c3h899/Diffuse_Light_Panel/Ideal_Model/3000-4500-6000 Response.png

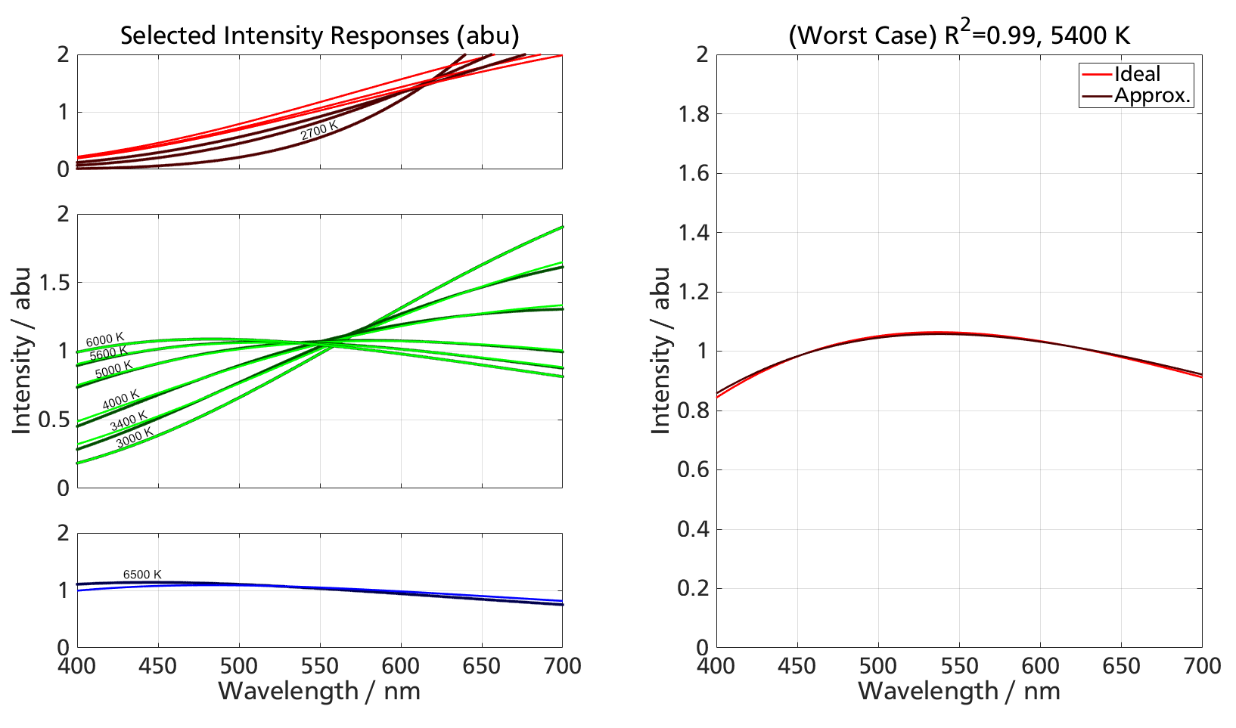
Ideal_Model/3000-4500-6000 Response.png
