c3h899/Diffuse_Light_Panel/Tri-Color LED/Preview/Cake-Pan-Ring.jpg

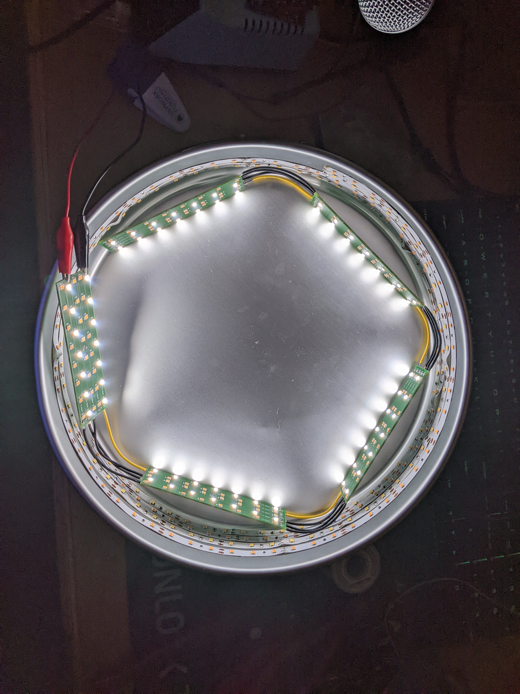
Tri-Color LED/Preview/Cake-Pan-Ring.jpg
