c3h899/Diffuse_Light_Panel/Tri-Color LED/Preview/Proto-Module.PNG

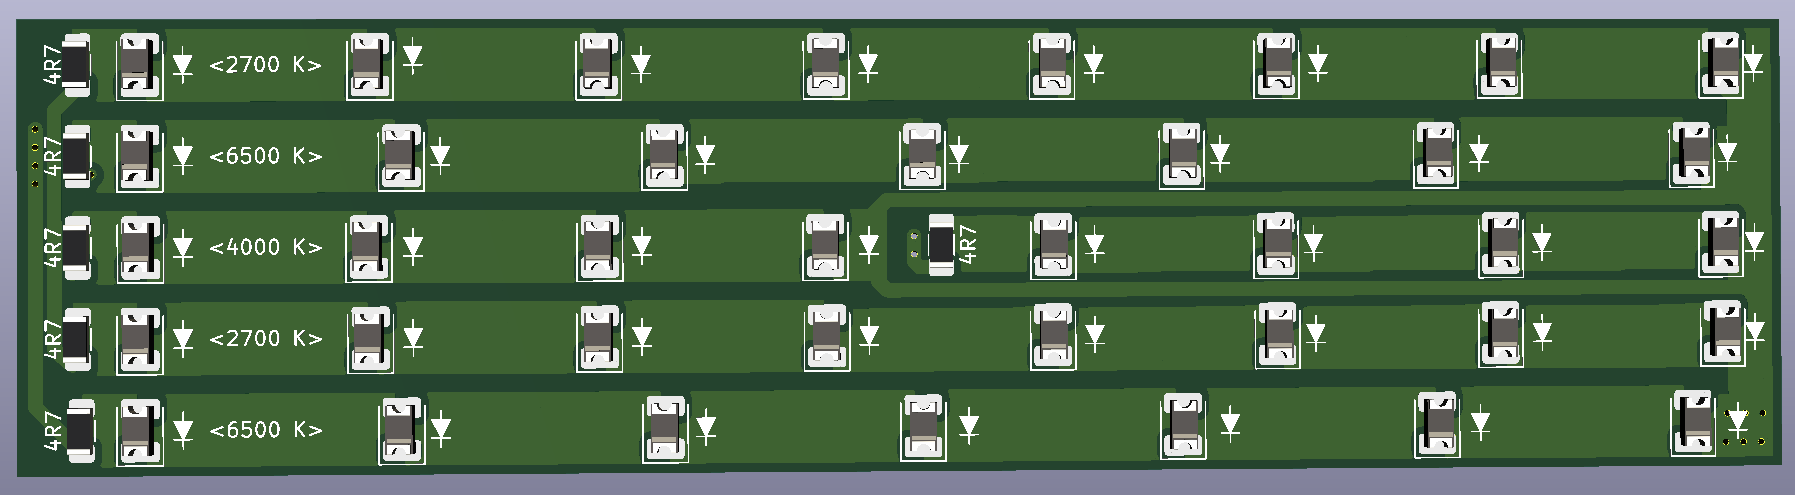
Tri-Color LED/Preview/Proto-Module.PNG
