c3h899/Diffuse_Light_Panel/LED_Measurements/5-foot Strip.PNG

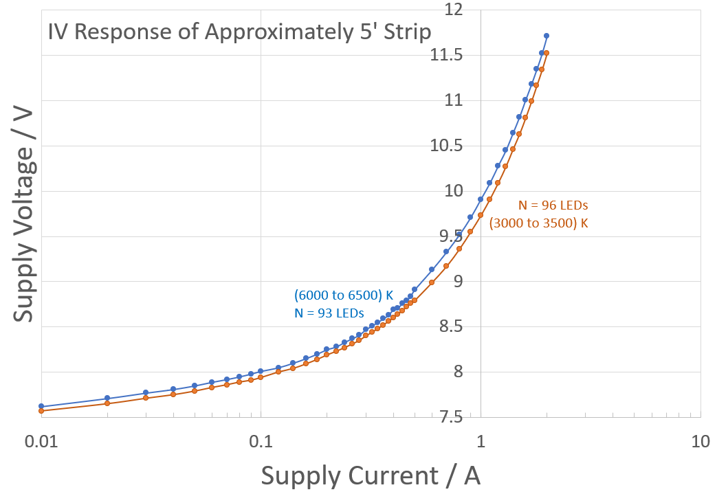
LED_Measurements/5-foot Strip.PNG
