c3h899/Diffuse_Light_Panel/LED_Measurements/Diode behavior.PNG

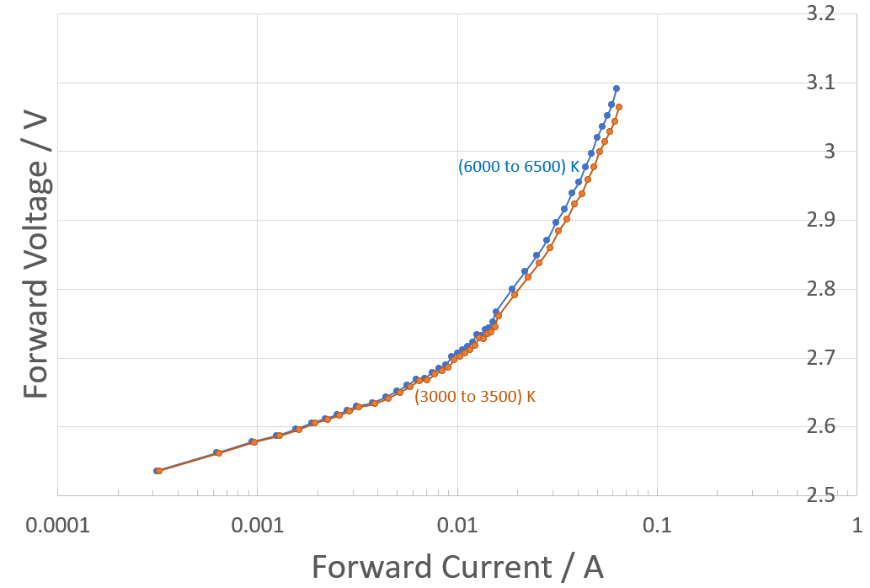
LED_Measurements/Diode behavior.PNG
